SuperHouse/ESPF/Images/ESPF-v3_0-front.jpg

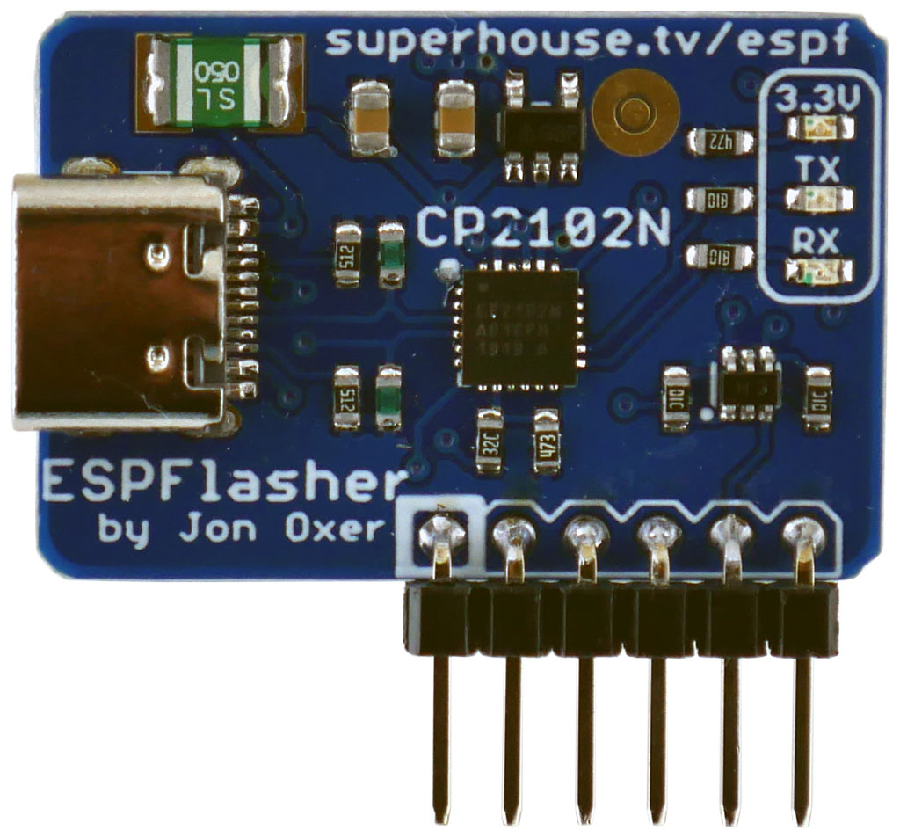
Images/ESPF-v3_0-front.jpg
